Ezhilkirthik/Frequency-Detector-using-OpAmp/Final_Circuit.asc

C1: cap; 10n
D2: diode; 1N4148
D3: diode; 1N4148
R1: res; 10K
R2: res; 1k
R3: res; 10k
R4: res; 10k
U1: UniversalOpAmp2
U3: LM741
V1: voltage; SINE(0 100m 2K)
V2: voltage; 15
V3: voltage; -15
Named nets: 0, V+, V-, Vin, Diff_out, Final_out
.tran 300m
